dczia/zippy-badge/Hardware/3d/SKRHABE010.STEP

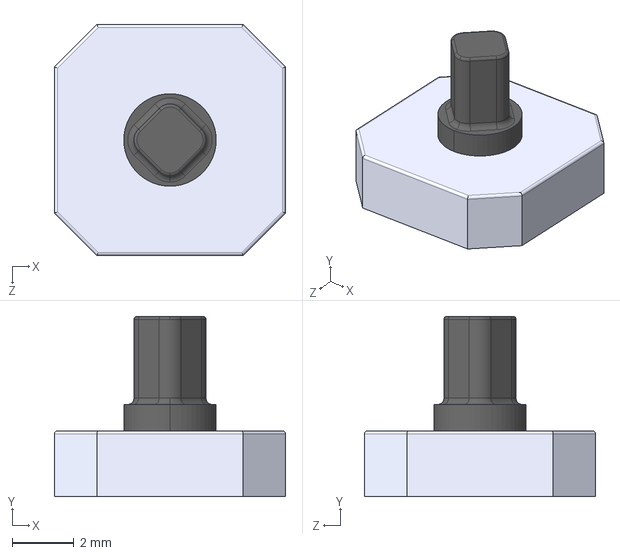
[picture p14: CAD file, 2025-06-01]
Hardware/3d/SKRHABE010.STEP
7.50 x 5.86 x 7.50 mm
