dczia/zippy-badge/Hardware/3d/3AAA Battery Box - Flying Leads.SLDPRT

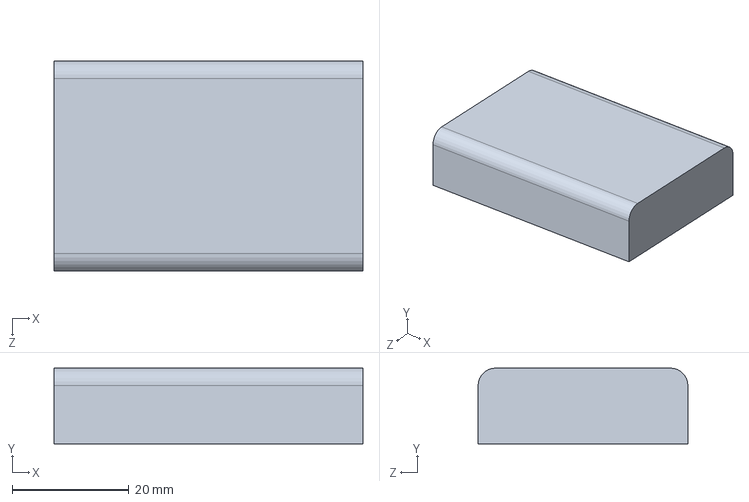
[picture p15: CAD file, 2025-04-25]
Hardware/3d/3AAA Battery Box - Flying Leads.SLDPRT
53.0 x 13.0 x 36.0 mm
