dczia/zippy-badge/Hardware/3d/EVQP7-JA-01P.STEP

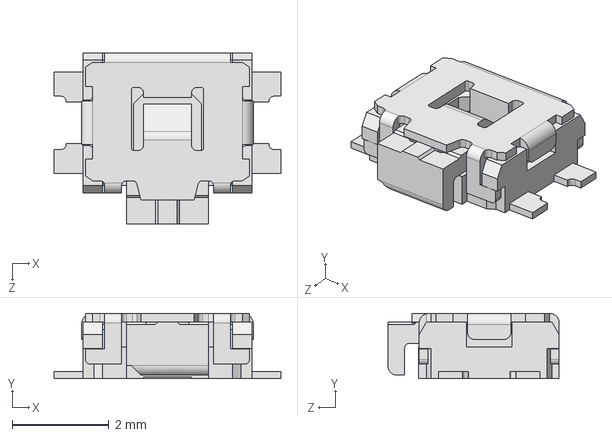
[picture p16: CAD file, 2025-04-25]
Hardware/3d/EVQP7-JA-01P.STEP
4.70 x 1.35 x 3.55 mm
