dczia/zippy-badge/Hardware/3d/MicroSD.STEP

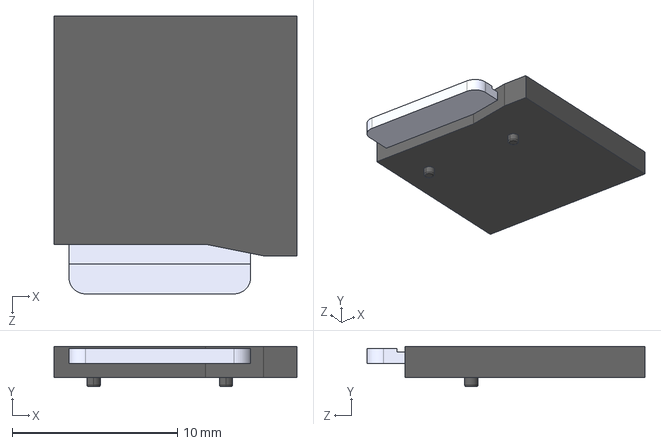
[picture p17: CAD file, 2025-04-25]
Hardware/3d/MicroSD.STEP
14.7 x 2.45 x 16.8 mm
